chrissabato/dakbot/webserver.py

# =============================================================================
# webserver.py — Async HTTP server: JSON data endpoint + settings UI
#
# Endpoints:
#   GET  /            → live scoreboard JSON
#   GET  /data        → same (alias)
#   GET  /settings    → settings form + device status (temp, RAM, uptime, IP)
#   POST /settings    → save settings to flash, redirect back
#   POST /reboot      → reboot the device
#   POST /update      → OTA update from GitHub
# =============================================================================

import uasyncio as asyncio
import ujson
import machine
import utime
import settings as _settings
import version as _version

score_data = {}
device_ip  = '—'          # set by main.py after Ethernet connects
_boot_ms   = utime.ticks_ms()


def dumps_sorted(d):
    """JSON-encode a flat dict with keys in sorted order.

    Unlike CPython 3.7+, MicroPython's dict does not preserve insertion
    order — dict(sorted(d.items())) sorts the intermediate list correctly,
    but wrapping it back into a dict discards that order again, and
    ujson.dumps() then just follows the dict's own (unordered) internal
    iteration order. Building the JSON text directly from the sorted list
    of pairs sidesteps dict ordering entirely: ujson.dumps() is only used
    here to correctly escape each individual key/value, while the actual
    assembly order comes from the list, which (unlike a dict) always
    preserves the order it's given.
    """
    return '{' + ','.join(
        ujson.dumps(k) + ':' + ujson.dumps(v) for k, v in sorted(d.items())
    ) + '}'


# =============================================================================
# Helpers
# =============================================================================

def _url_decode(s):
    s = s.replace('+', ' ')
    out = []
    i = 0
    while i < len(s):
        if s[i] == '%' and i + 2 < len(s):
            out.append(chr(int(s[i+1:i+3], 16)))
            i += 3
        else:
            out.append(s[i])
            i += 1
    return ''.join(out)


def _parse_form(body):
    if isinstance(body, (bytes, bytearray)):
        body = body.decode('utf-8')
    data = {}
    for pair in body.split('&'):
        if '=' in pair:
            k, v = pair.split('=', 1)
            data[_url_decode(k)] = _url_decode(v)
    return data


def _clean_hostname(value):
    """Strip a URL scheme, path, and trailing slashes so a pasted URL
    (e.g. https://broker.example.com/) still saves as a bare hostname —
    the raw socket connect in mqtt_publisher.py needs just the host."""
    value = value.strip()
    if '://' in value:
        value = value.split('://', 1)[1]
    value = value.split('/', 1)[0]
    return value


async def _send(writer, status, content_type, body):
    if isinstance(body, str):
        body = body.encode('utf-8')
    writer.write(
        b'HTTP/1.0 ' + status + b'\r\n'
        b'Content-Type: ' + content_type + b'\r\n'
        b'Content-Length: ' + str(len(body)).encode() + b'\r\n'
        b'Access-Control-Allow-Origin: *\r\n'
        b'Cache-Control: no-store, no-cache, must-revalidate\r\n'
        b'Connection: close\r\n\r\n'
    )
    writer.write(body)
    await writer.drain()


async def _redirect(writer, location):
    writer.write(
        b'HTTP/1.0 303 See Other\r\n'
        b'Location: ' + location.encode() + b'\r\n'
        b'Content-Length: 0\r\n'
        b'Connection: close\r\n\r\n'
    )
    await writer.drain()


# =============================================================================
# Settings page HTML
# =============================================================================

_CSS = (
    '*{box-sizing:border-box;margin:0;padding:0}'
    'body{font-family:sans-serif;background:#f0f2f5;color:#222;padding:1rem;max-width:520px;margin:0 auto}'
    'h1{font-size:1.3rem;font-weight:700;margin-bottom:1rem;color:#111}'
    '.card{background:#fff;border-radius:8px;padding:1.25rem;margin-bottom:1rem;box-shadow:0 1px 3px rgba(0,0,0,.1)}'
    'h2{font-size:.75rem;font-weight:700;text-transform:uppercase;letter-spacing:.06em;color:#888;margin-bottom:1rem}'
    'label{display:block;font-size:.875rem;font-weight:500;margin-bottom:.3rem;color:#333}'
    'input[type=text],input[type=number],select{width:100%;padding:.5rem .75rem;border:1px solid #ddd;'
    'border-radius:6px;font-size:.9rem;margin-bottom:.9rem;background:#fafafa}'
    'input[type=text]:focus,input[type=number]:focus,select:focus{outline:none;border-color:#2563eb;background:#fff}'
    '.check-row{display:flex;align-items:center;gap:.6rem;margin-bottom:.9rem}'
    '.check-row input{width:1rem;height:1rem;margin:0}'
    '.check-row label{margin:0;font-weight:400}'
    '.btn{display:inline-block;padding:.6rem 1.4rem;border:none;border-radius:6px;'
    'font-size:.9rem;font-weight:600;cursor:pointer}'
    '.btn-primary{background:#2563eb;color:#fff}'
    '.btn-danger{background:#dc2626;color:#fff}'
    '.note{font-size:.8rem;color:#888;margin-top:.6rem;line-height:1.4}'
    '.banner{padding:.75rem 1rem;border-radius:6px;margin-bottom:1rem;font-size:.875rem}'
    '.ok{background:#dcfce7;color:#166534;border:1px solid #bbf7d0}'
    '.err{background:#fee2e2;color:#991b1b;border:1px solid #fecaca}'
)

_update_error = None   # set by _do_update() on a failed OTA; shown as a banner on /settings

def _dashboard_html():
    import gc
    gc.collect()
    try:
        import esp32
        temp = '{}\u00b0C'.format(esp32.mcu_temperature())
    except Exception:
        temp = '—'
    uptime_s  = utime.ticks_diff(utime.ticks_ms(), _boot_ms) // 1000
    h, rem    = divmod(uptime_s, 3600)
    m, sec    = divmod(rem, 60)
    uptime    = '{}h {}m {}s'.format(h, m, sec)
    free_kb   = gc.mem_free()  // 1024
    total_kb  = (gc.mem_free() + gc.mem_alloc()) // 1024
    console   = score_data.get('console', 'daktronics')
    sport     = score_data.get('sport', '—')
    dev_name  = score_data.get('device_name', '—')

    def row(label, value):
        return (
            '<span style="opacity:.55">{}</span>'
            '<span style="font-weight:500">{}</span>'
        ).format(label, value)

    if console == 'colorado':
        status_extra = (
            row('Event', score_data.get('EventNumber', '—'))
            + row('Heat',  score_data.get('HeatNumber', '—'))
            + row('Clock', score_data.get('Clock', '—'))
        )
    else:
        status_extra = row('Sport', sport)

    return (
        '<div class="card"><h2>Device Status</h2>'
        '<div style="display:grid;grid-template-columns:auto 1fr;gap:.5rem .75rem;font-size:.875rem">'
        + row('Device Name', dev_name)
        + row('IP Address', device_ip)
        + status_extra
        + row('Version', '<span id="dash-ver">' + str(_version.VERSION) + '</span>')
        + row('MCU Temp',   temp)
        + row('Free RAM',   '{} KB / {} KB'.format(free_kb, total_kb))
        + row('Uptime',     uptime)
        + '</div>'
        '<p class="note" style="margin-top:.75rem">Reload the page to refresh.</p>'
        '</div>'
    )


def _mqtt_html(s):
    chk     = ' checked' if s.get('mqtt_enabled') else ''
    hidden  = '' if s.get('mqtt_enabled') else ' style="display:none"'
    return (
        '<div class="card"><h2>MQTT</h2>'
        '<div class="check-row">'
        '<input type="checkbox" name="mqtt_enabled" id="mqtt_en"' + chk +
        ' onchange="document.getElementById(\'mqttcfg\').style.display=this.checked?\'\':\'none\';">'
        '<label for="mqtt_en">Enable MQTT publishing</label>'
        '</div>'
        '<div id="mqttcfg"' + hidden + '>'
        '<label>Broker hostname</label>'
        '<input type="text" name="mqtt_broker" value="' + s.get('mqtt_broker', '') + '" '
        'placeholder="xxxx.s1.eu.hivemq.cloud">'
        '<label>Port (TLS)</label>'
        '<input type="number" name="mqtt_port" value="' + str(s.get('mqtt_port', 8883)) + '">'
        '<label>Username</label>'
        '<input type="text" name="mqtt_user" value="' + s.get('mqtt_user', '') + '">'
        '<label>Password</label>'
        '<input type="text" name="mqtt_password" value="' + s.get('mqtt_password', '') + '">'
        '<label>Topic</label>'
        '<input type="text" name="mqtt_topic" value="' + s.get('mqtt_topic', '') + '" '
        'placeholder="' + _settings._default_mqtt_topic() + '">'
        '<p class="note">Defaults to a per-device topic (dakbot/score/&lt;MAC&gt;) if left blank. '
        'Requires umqtt.simple on the device. '
        'Install once: <code>mpremote mip install umqtt.simple</code>. '
        'Reboot required after changing.</p>'
        '</div>'
        '</div>'
    )


def _settings_html(saved=False):
    s = _settings.current
    console_val = s.get('console', 'daktronics')
    consoles = [
        ('daktronics', 'Daktronics AllSport 5000'),
        ('colorado',   'Colorado System 7 (Swim Timing)'),
    ]
    console_opts = ''.join(
        '<option value="{}"{}>{}</option>'.format(
            v, ' selected' if console_val == v else '', lbl
        )
        for v, lbl in consoles
    )
    sport_hidden = ' style="display:none"' if console_val == 'colorado' else ''
    sports = [
        ('baseball',       'Baseball'),
        ('basketball',     'Basketball'),
        ('volleyball',     'Volleyball'),
        ('football',       'Football'),
        ('hockeylacrosse', 'Hockey / Lacrosse'),
    ]
    opts = ''.join(
        '<option value="{}"{}>{}</option>'.format(
            v, ' selected' if s['sport'] == v else '', lbl
        )
        for v, lbl in sports
    )
    chk    = ' checked' if s.get('use_dhcp') else ''
    hidden = ' style="display:none"' if s.get('use_dhcp') else ''
    banner = (
        '<div class="banner ok">Settings saved — reboot to apply console, sport, network, or pin changes.</div>'
        if saved else ''
    )
    if _update_error:
        banner += '<div class="banner err">' + _update_error + '</div>'

    return (
        '<!DOCTYPE html><html><head>'
        '<meta charset="utf-8">'
        '<meta name="viewport" content="width=device-width,initial-scale=1">'
        '<title>Dakbot Settings</title>'
        '<style>' + _CSS + '</style>'
        '</head><body>'
        '<h1>Dakbot Settings</h1>'
        + banner
        + _dashboard_html() +

        # ---- Identity ----------------------------------------------------------
        '<form method="POST" action="/settings">'
        '<div class="card"><h2>Identity</h2>'
        '<label>Device Name</label>'
        '<input type="text" name="device_name" value="' + s.get('device_name', '') + '" '
        'placeholder="' + _settings._default_device_name() + '">'
        '<p class="note">Defaults to the device\'s MAC address if left blank.</p>'
        '</div>'

        # ---- Console -----------------------------------------------------------
        '<div class="card"><h2>Console</h2>'
        '<label for="console_type">Console type</label>'
        '<select name="console" id="console_type" '
        'onchange="document.getElementById(\'sportcard\').style.display='
        'this.value==\'colorado\'?\'none\':\'\';">'
        + console_opts +
        '</select>'
        '</div>'

        # ---- Sport -----------------------------------------------------------
        '<div class="card" id="sportcard"' + sport_hidden + '><h2>Sport</h2>'
        '<label for="sport">Active sport</label>'
        '<select name="sport" id="sport">' + opts + '</select>'
        '</div>'

        # ---- Network ---------------------------------------------------------
        '<div class="card"><h2>Network</h2>'
        '<div class="check-row">'
        '<input type="checkbox" name="use_dhcp" id="dhcp"' + chk +
        ' onchange="document.getElementById(\'st\').style.display=this.checked?\'none\':\'\';">'
        '<label for="dhcp">Use DHCP</label>'
        '</div>'
        '<div id="st"' + hidden + '>'
        '<label>IP Address</label>'
        '<input type="text" name="ip" value="' + s.get('ip', '') + '">'
        '<label>Subnet Mask</label>'
        '<input type="text" name="mask" value="' + s.get('mask', '') + '">'
        '<label>Gateway</label>'
        '<input type="text" name="gateway" value="' + s.get('gateway', '') + '">'
        '<label>DNS Server</label>'
        '<input type="text" name="dns" value="' + s.get('dns', '') + '">'
        '</div>'
        '<label>HTTP Port</label>'
        '<input type="number" name="http_port" value="' + str(s.get('http_port', 80)) + '">'
        '</div>'

        # ---- Serial ----------------------------------------------------------
        '<div class="card"><h2>Serial</h2>'
        '<label>UART RX Pin (GPIO number)</label>'
        '<input type="number" name="uart_rx" value="' + str(s.get('uart_rx', 16)) + '">'
        '<p class="note">Wire the active console\'s serial output (via MAX3232 level shifter) '
        'to this GPIO — AllSport 5000 RTD, or Colorado System 7, depending on Console Type above. '
        'Reboot required after changing.</p>'
        '</div>'

        # ---- MQTT ------------------------------------------------------------
        + _mqtt_html(s) +

        # ---- Save ------------------------------------------------------------
        '<div class="card"><h2>Save</h2>'
        '<button type="submit" class="btn btn-primary">Save Settings</button>'
        '<p class="note">Console, sport, network, and pin changes require a reboot to take effect.</p>'
        '</div>'
        '</form>'

        # ---- Reboot / Update -------------------------------------------------
        '<form method="POST" action="/reboot"'
        ' onsubmit="return confirm(\'Reboot the device now?\');">'
        '<div class="card"><h2>Device</h2>'
        '<button type="submit" class="btn btn-danger">Reboot Device</button>'
        '<p class="note">Applies all saved settings and restarts the firmware.</p>'
        '</div>'
        '</form>'

        '<div class="card"><h2>Firmware Update</h2>'
        '<p id="ver-status" class="note">Checking for updates\u2026</p>'
        '<form id="update-form" method="POST" action="/update" style="display:none;margin-top:.75rem"'
        ' onsubmit="this.querySelector(\'button\').disabled=true;'
        'this.querySelector(\'button\').textContent=\'Updating\u2026\';return true;">'
        '<button type="submit" class="btn btn-primary">Update from GitHub</button>'
        '<p class="note" style="margin-top:.5rem">Downloads the latest code and reboots automatically. '
        'settings.json is preserved.</p>'
        '</form>'
        '<form method="POST" action="/update" style="margin-top:.75rem"'
        ' onsubmit="if(!confirm(\'Reinstall firmware from GitHub now, even though it reports up to date?\'))'
        '{return false;}'
        'this.querySelector(\'button\').disabled=true;'
        'this.querySelector(\'button\').textContent=\'Updating…\';return true;">'
        '<button type="submit" class="btn" style="background:#e5e7eb;color:#374151">Force Reinstall</button>'
        '<p class="note" style="margin-top:.5rem">Re-downloads every file from GitHub and reboots, '
        'regardless of the version check above. Useful if a previous update partially failed.</p>'
        '</form>'
        '<script>'
        '(function(){'
        'var cur=' + str(_version.VERSION) + ';'
        'fetch("https://api.github.com/repos/chrissabato/dakbot/contents/version.py",'
        '{cache:"no-store",headers:{"Accept":"application/vnd.github.raw"}})'
        '.then(function(r){return r.text();})'
        '.then(function(t){'
        'var m=t.match(/VERSION\\s*=\\s*(\\d+)/);'
        'var latest=m?parseInt(m[1]):null;'
        'var msg=document.getElementById("ver-status");'
        'var form=document.getElementById("update-form");'
        'if(latest===null){msg.textContent="Could not parse version. Raw: "+t.slice(0,80);form.style.display="";}'
        'else if(latest>cur){'
        'msg.textContent="Version "+latest+" available (installed: "+cur+").";'
        'form.style.display="";'
        'var dv=document.getElementById("dash-ver");'
        'if(dv)dv.innerHTML=cur+" \u26a0\ufe0f update available";'
        '}'
        'else{msg.textContent="Up to date \u2713 (installed: "+cur+", latest: "+latest+")";}'
        '})'
        '.catch(function(e){document.getElementById("ver-status").textContent="Fetch error: "+e;'
        'document.getElementById("update-form").style.display="";});'
        '})()'
        '</script>'
        '</div>'

        '</body></html>'
    )


# =============================================================================
# Route handlers
# =============================================================================

async def _handle_settings_get(writer, saved=False):
    await _send(writer, b'200 OK', b'text/html; charset=utf-8', _settings_html(saved))


async def _handle_settings_post(writer, body):
    form = _parse_form(body)
    _settings.save({
        'device_name':   form.get('device_name', _settings.current.get('device_name', '')),
        'console':       form.get('console', _settings.current.get('console', 'daktronics')),
        'sport':         form.get('sport', _settings.DEFAULTS['sport']),
        'use_dhcp':      'use_dhcp' in form,
        'ip':            form.get('ip',        _settings.current.get('ip', '')),
        'mask':          form.get('mask',      _settings.current.get('mask', '')),
        'gateway':       form.get('gateway',   _settings.current.get('gateway', '')),
        'dns':           form.get('dns',       _settings.current.get('dns', '')),
        'uart_rx':       int(form.get('uart_rx',   _settings.current.get('uart_rx', 16))),
        'http_port':     int(form.get('http_port', _settings.current.get('http_port', 80))),
        'mqtt_enabled':  'mqtt_enabled' in form,
        'mqtt_broker':   _clean_hostname(form.get('mqtt_broker', _settings.current.get('mqtt_broker', ''))),
        'mqtt_port':     int(form.get('mqtt_port', _settings.current.get('mqtt_port', 8883))),
        'mqtt_user':     form.get('mqtt_user',     _settings.current.get('mqtt_user', '')),
        'mqtt_password': form.get('mqtt_password', _settings.current.get('mqtt_password', '')),
        'mqtt_topic':    form.get('mqtt_topic',    _settings.current.get('mqtt_topic', '')),
    })
    await _redirect(writer, '/settings?saved=1')


async def _do_update():
    """Background task: run updater then reboot. Runs after response is sent.
    Only reboots on a fully successful update — updater.update_all() leaves
    the previous firmware untouched on flash if any file failed to
    download, so rebooting on a partial failure would be safe too, but
    there's nothing to gain by doing so and it'd cost the (functioning) old
    process. update_all() is documented to never raise, but this task has
    nothing else to catch an unexpected exception — one escaping silently
    kills the task with no reboot and no error banner, which is worse than
    a wrong-but-visible message, so it's wrapped defensively anyway."""
    global _update_error
    await asyncio.sleep_ms(500)   # ensure response is flushed first
    import updater
    try:
        ok, results = updater.update_all()
    except Exception as ex:
        ok, results = False, [('(unexpected)', False, str(ex))]

    if ok:
        _update_error = None
        machine.reset()
    else:
        failed = [f for f, file_ok, detail in results if not file_ok]
        _update_error = 'Update failed — firmware may be unchanged. Problem files: ' + ', '.join(failed)
        print('OTA update failed, not rebooting:', results)


async def _handle_update(writer):
    # Send the response immediately — the actual download happens in a background
    # task so the event loop is free to flush the response before blocking I/O starts.
    body = (
        '<!DOCTYPE html><html><head><meta charset="utf-8">'
        '<meta name="viewport" content="width=device-width,initial-scale=1">'
        '<meta http-equiv="refresh" content="45;url=/settings">'
        '<style>body{font-family:sans-serif;background:#f0f2f5;padding:2rem;'
        'max-width:520px;margin:0 auto;text-align:center}'
        'h2{margin-bottom:1rem}.note{color:#666;font-size:.9rem;line-height:1.6}'
        '</style></head><body>'
        '<h2>Updating firmware\u2026</h2>'
        '<p class="note">Downloading files from GitHub and writing to flash.<br>'
        'The device will reboot automatically when complete.<br>'
        'This page will redirect to settings in ~45 seconds.</p>'
        '</body></html>'
    )
    await _send(writer, b'200 OK', b'text/html; charset=utf-8', body)
    asyncio.create_task(_do_update())


async def _handle_reboot(writer):
    await _send(
        writer, b'200 OK', b'text/html; charset=utf-8',
        '<!DOCTYPE html><html><head><meta charset="utf-8">'
        '<style>body{font-family:sans-serif;padding:2rem;max-width:400px;margin:0 auto}</style>'
        '<script>setTimeout(()=>{location.href="/settings"},6000)</script>'
        '</head><body>'
        '<h2>Rebooting&hellip;</h2>'
        '<p>The device is restarting. Redirecting to settings in a few seconds.</p>'
        '</body></html>'
    )
    await asyncio.sleep_ms(300)
    machine.reset()


# =============================================================================
# Main request dispatcher
# =============================================================================

async def _handle_client(reader, writer):
    try:
        request_line = await asyncio.wait_for(reader.readline(), timeout=3)
        parts  = request_line.split()
        method = parts[0].decode() if len(parts) >= 1 else 'GET'
        path   = parts[1].decode() if len(parts) >= 2 else '/'

        # Read headers, pick up Content-Length
        content_length = 0
        while True:
            line = await asyncio.wait_for(reader.readline(), timeout=3)
            if line in (b'\r\n', b'', b'\n'):
                break
            if line.lower().startswith(b'content-length:'):
                content_length = int(line.split(b':')[1].strip())

        # Read POST body
        body = b''
        if method == 'POST' and content_length > 0:
            body = await asyncio.wait_for(reader.read(content_length), timeout=5)

        # Route
        base  = path.split('?')[0]
        saved = 'saved=1' in path

        if base in ('/', '/data'):
            await _send(writer, b'200 OK', b'application/json',
                        '[' + dumps_sorted(score_data) + ']')
        elif base == '/settings' and method == 'GET':
            await _handle_settings_get(writer, saved=saved)
        elif base == '/settings' and method == 'POST':
            await _handle_settings_post(writer, body)
        elif base == '/update' and method == 'POST':
            await _handle_update(writer)
        elif base == '/reboot' and method == 'POST':
            await _handle_reboot(writer)
        else:
            await _send(writer, b'404 Not Found', b'application/json', '{"error":"not found"}')

    except Exception as e:
        print('HTTP error:', e)
    finally:
        writer.close()
        await writer.wait_closed()


# =============================================================================
# Server startup
# =============================================================================

async def start(port=80):
    server = await asyncio.start_server(_handle_client, '0.0.0.0', port)
    print('HTTP server listening on port', port)
    return server
